imsenthur/Arboc/mechanicalDesign/solidworks/step/metalHorn.step

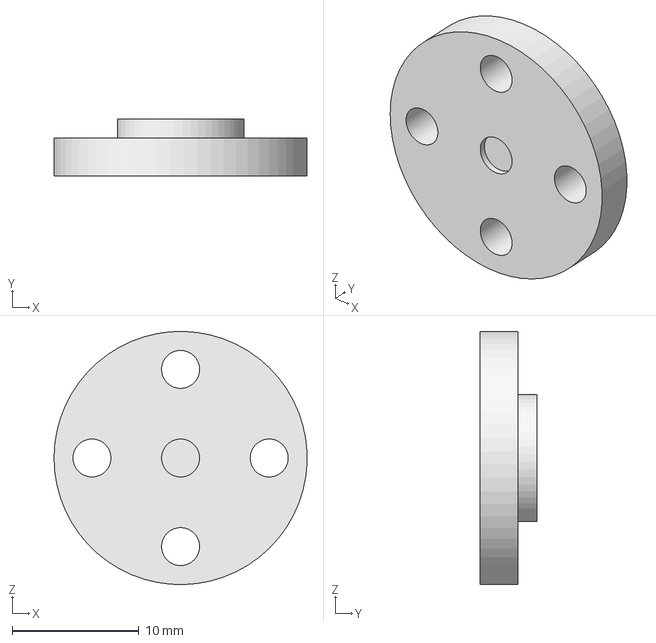
[picture p18: CAD file, 2018-06-01]
mechanicalDesign/solidworks/step/metalHorn.step
20.0 x 4.50 x 20.0 mm
