imsenthur/Arboc/mechanicalDesign/3DprintedParts/type4.step

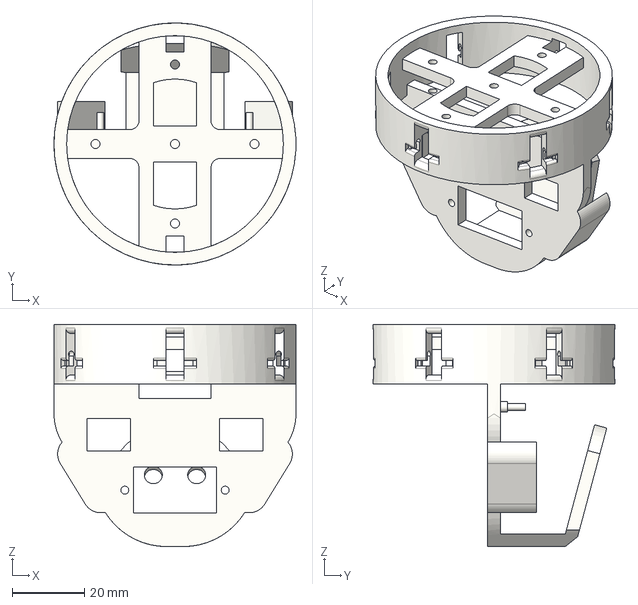
[picture p19: CAD file, 2018-02-13]
mechanicalDesign/3DprintedParts/type4.step
67.0 x 67.0 x 61.5 mm
