imsenthur/Arboc/mechanicalDesign/solidworks/iges/tailLink.SLDPRT

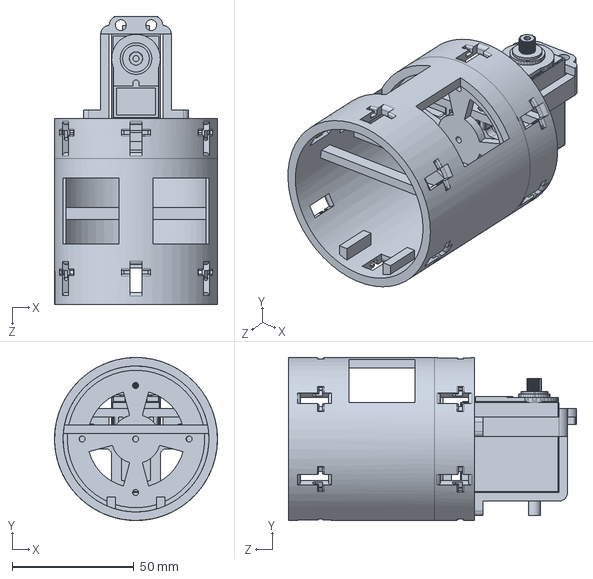
[picture p20: CAD file, 2018-03-31]
mechanicalDesign/solidworks/iges/tailLink.SLDPRT
67.0 x 67.0 x 118.5 mm
