imsenthur/Arboc/mechanicalDesign/solidworks/sldprt/tailNew.SLDPRT

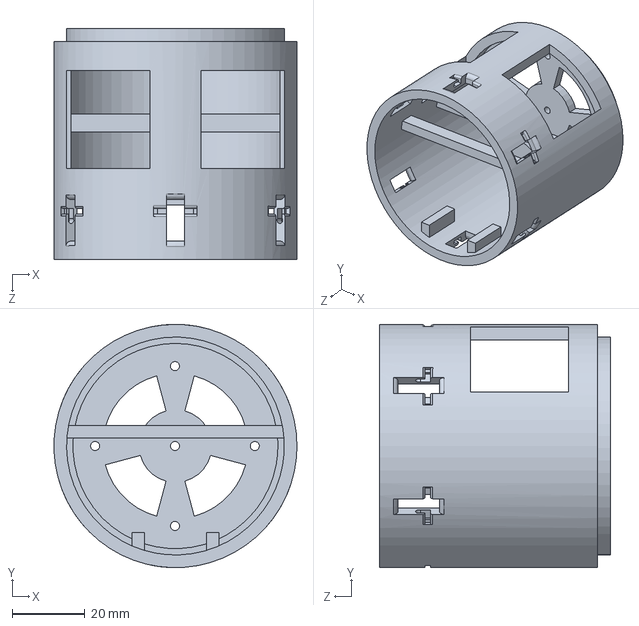
[picture p21: CAD file, 2018-03-30]
mechanicalDesign/solidworks/sldprt/tailNew.SLDPRT
66.9 x 67.0 x 63.5 mm
