imsenthur/Arboc/mechanicalDesign/solidworks/step/lowerBracket.step

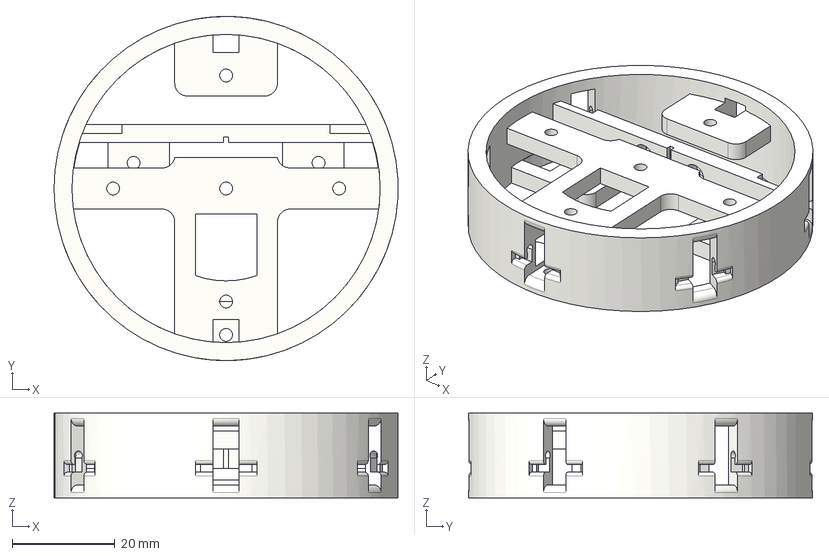
[picture p22: CAD file, 2018-06-01]
mechanicalDesign/solidworks/step/lowerBracket.step
67.0 x 67.0 x 16.5 mm
