imsenthur/Arboc/simulationExports/gazebo/stl/end.stl

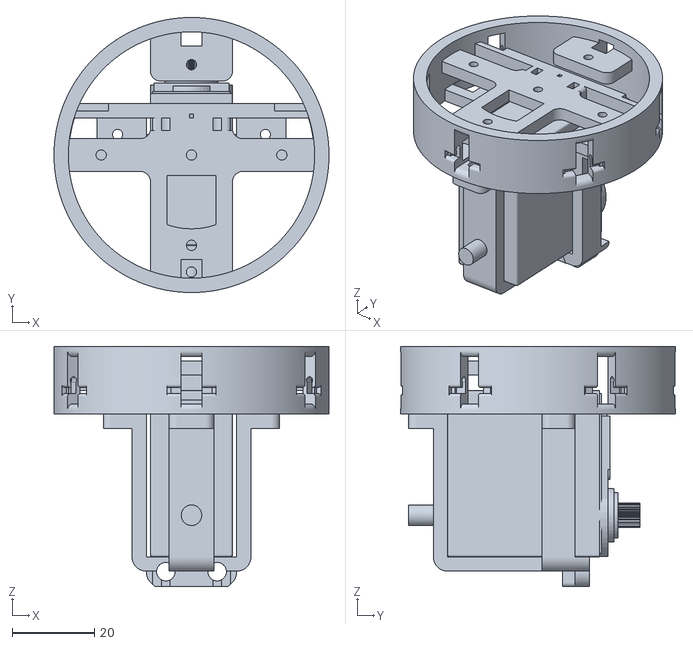
[picture p23: CAD file, 2018-07-22]
simulationExports/gazebo/stl/end.stl
67.0 x 67.0 x 58.5
