imsenthur/Arboc/simulationExports/vrep/stl/moduleCollider.stl

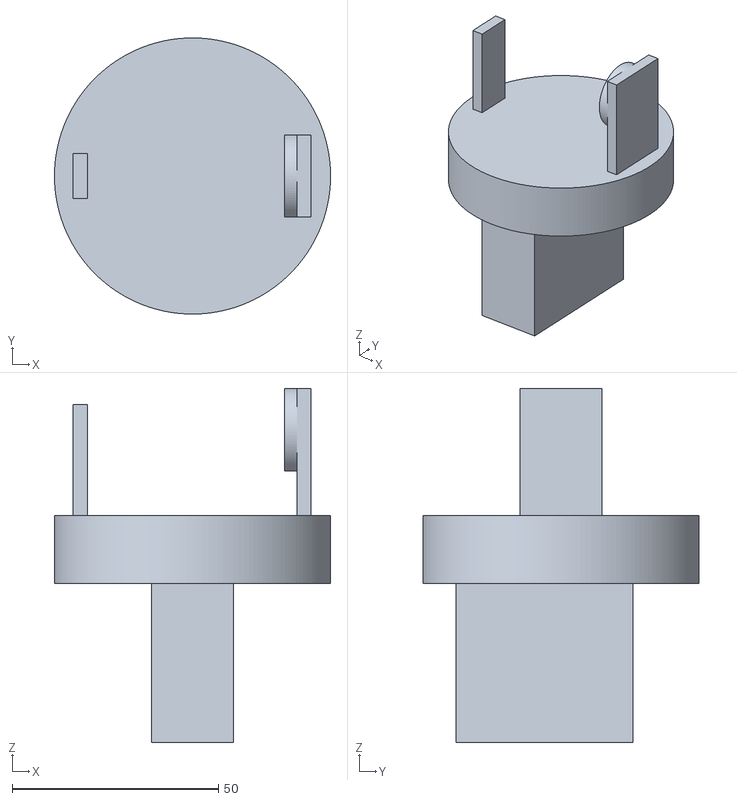
[picture p24: CAD file, 2018-05-26]
simulationExports/vrep/stl/moduleCollider.stl
67.0 x 67.0 x 85.9
