imsenthur/Arboc/mechanicalDesign/solidworks/step/middleBracket.step

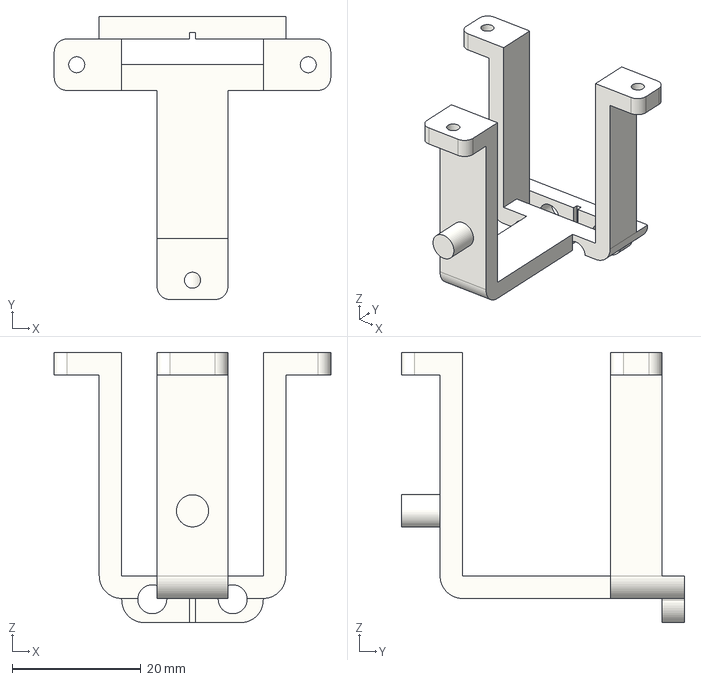
[picture p26: CAD file, 2018-06-01]
mechanicalDesign/solidworks/step/middleBracket.step
43.0 x 44.0 x 42.0 mm
