imsenthur/Arboc/mechanicalDesign/3DprintedParts/type6.step

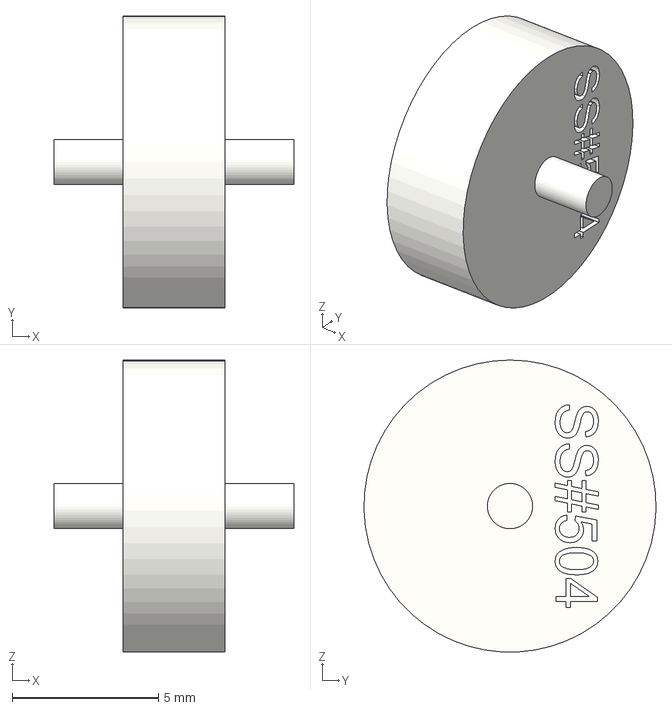
[picture p27: CAD file, 2018-02-13]
mechanicalDesign/3DprintedParts/type6.step
8.20 x 10.00 x 9.99 mm
