imsenthur/Arboc/mechanicalDesign/solidworks/sldprt/headMod.SLDPRT

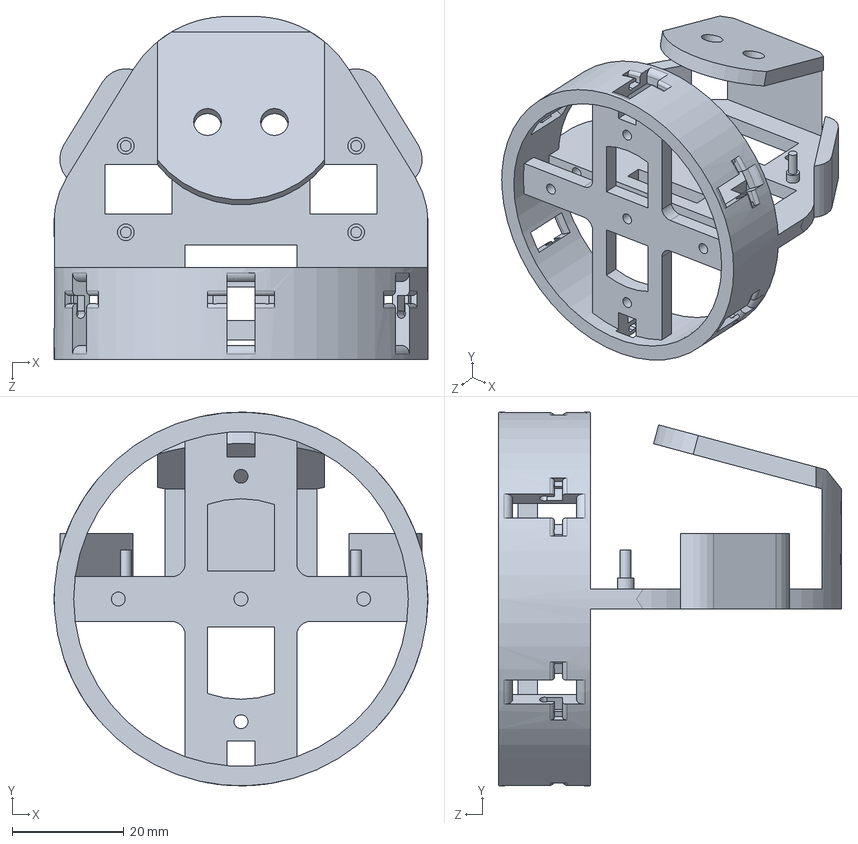
[picture p28: CAD file, 2018-03-30]
mechanicalDesign/solidworks/sldprt/headMod.SLDPRT
67.0 x 67.0 x 61.5 mm
