imsenthur/Arboc/simulationExports/vrep/stl/tailCollider.stl

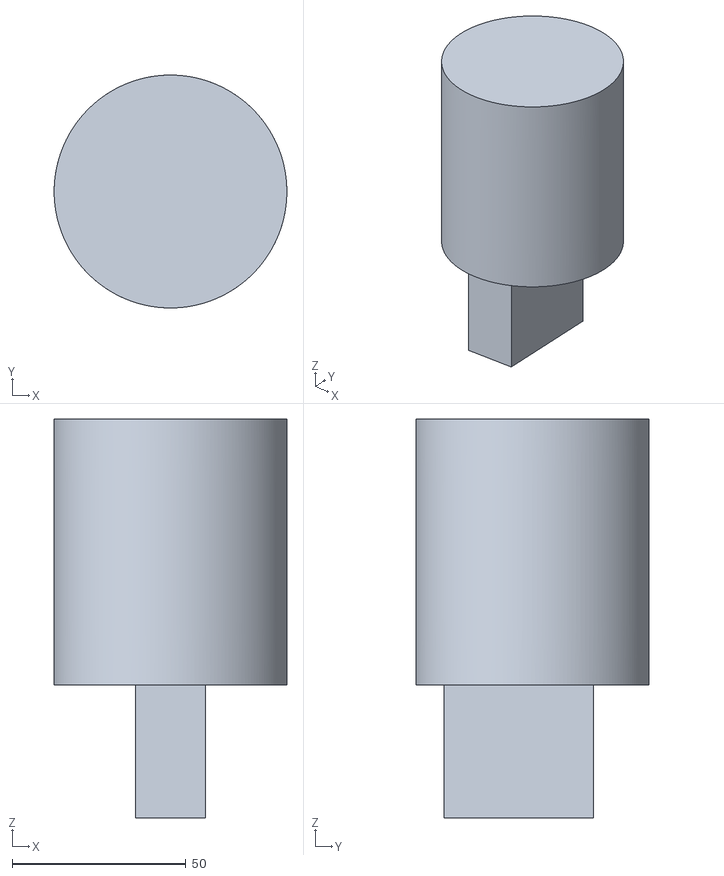
[picture p29: CAD file, 2018-05-26]
simulationExports/vrep/stl/tailCollider.stl
66.9 x 67.0 x 114.8
