imsenthur/Arboc/mechanicalDesign/solidworks/step/servo.step

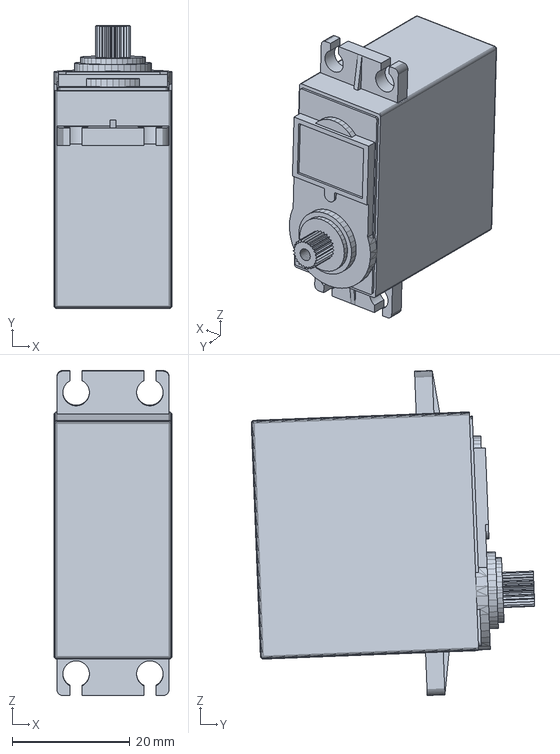
[picture p30: CAD file, 2018-06-01]
mechanicalDesign/solidworks/step/servo.step
20.0 x 48.1 x 55.1 mm
