imsenthur/Arboc/simulationExports/vrep/stl/headCollider.stl

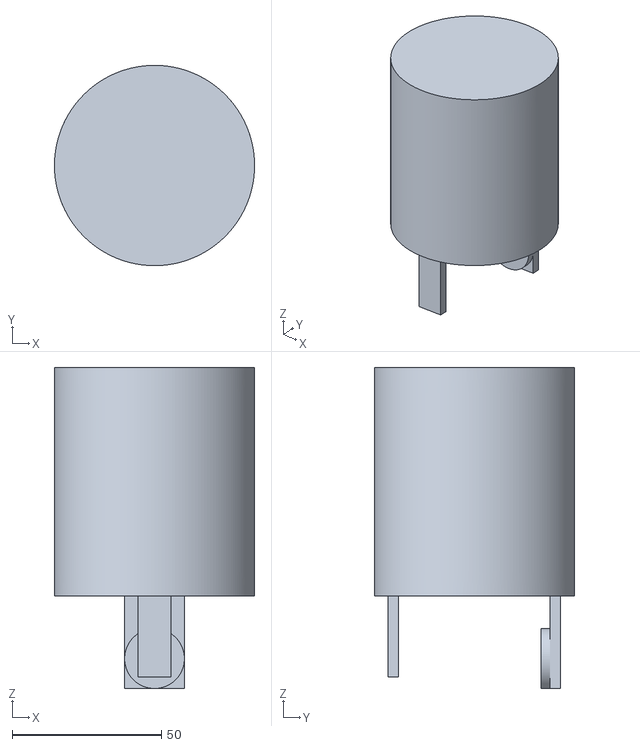
[picture p31: CAD file, 2018-05-26]
simulationExports/vrep/stl/headCollider.stl
66.9 x 67.0 x 107.4
