imsenthur/Arboc/mechanicalDesign/solidworks/step/upperBracket.step

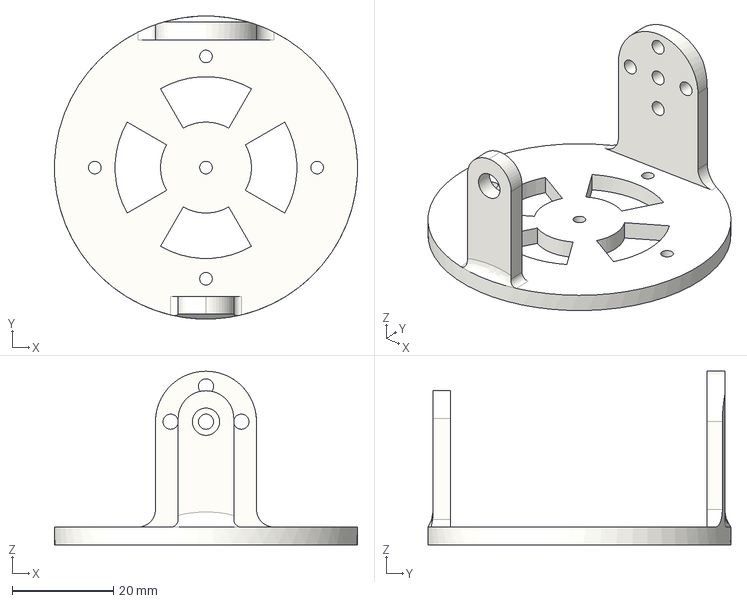
[picture p32: CAD file, 2018-06-01]
mechanicalDesign/solidworks/step/upperBracket.step
60.0 x 60.0 x 34.4 mm
